samregardie/449Project/lab3/stm32/include/current.h

#ifndef CURRENT_H
#define CURRENT_H

// Same order as io-channels in app.overlay: i_right, i_left, i_servo
enum current_sensor
{
    MOTOR_RIGHT = 0,
    MOTOR_LEFT = 1,
    SERVO = 2
};

int current_sense_init(void);

int print_all_currents(void);

// Return the current passing through the given sensor, rounded to the
// nearest mA.
// Note that current can be negative based on direction.
int get_current(enum current_sensor sensor);

#endif
